MarSik/BuildingAccessSystem/controller/src/include/etl_profile.h

///\file

/******************************************************************************
The MIT License(MIT)

Embedded Template Library.
https://github.com/ETLCPP/etl
https://www.etlcpp.com

Copyright(c) 2017 jwellbelove

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
THE SOFTWARE IS PROVIDED "AS IS", WITHOUT WARRANTY OF ANY KIND, EXPRESS OR
IMPLIED, INCLUDING BUT NOT LIMITED TO THE WARRANTIES OF MERCHANTABILITY,
FITNESS FOR A PARTICULAR PURPOSE AND NONINFRINGEMENT.IN NO EVENT SHALL THE
AUTHORS OR COPYRIGHT HOLDERS BE LIABLE FOR ANY CLAIM, DAMAGES OR OTHER
LIABILITY, WHETHER IN AN ACTION OF CONTRACT, TORT OR OTHERWISE, ARISING FROM,
OUT OF OR IN CONNECTION WITH THE SOFTWARE OR THE USE OR OTHER DEALINGS IN THE
SOFTWARE.
******************************************************************************/

#ifndef __ETL_GCC__
#define __ETL_GCC__

//*****************************************************************************
// GCC
//*****************************************************************************

#include <limits.h>

#define ETL_TARGET_DEVICE_GENERIC
#define ETL_TARGET_OS_NONE
#define ETL_COMPILER_GCC
#define ETL_CPP11_SUPPORTED                        (__cplusplus >= 201103L)
#define ETL_CPP14_SUPPORTED                        (__cplusplus >= 201402L)
#define ETL_NO_NULLPTR_SUPPORT                     !ETL_CPP11_SUPPORTED
#define ETL_NO_LARGE_CHAR_SUPPORT                  !ETL_CPP11_SUPPORTED
#define ETL_CPP11_TYPE_TRAITS_IS_TRIVIAL_SUPPORTED ETL_CPP14_SUPPORTED
#define ETL_ATOMIC_SUPPORTED                       ETL_CPP11_SUPPORTED

#define ETL_NO_CHECKS

#endif
