MarSik/BuildingAccessSystem/controller/src/countdown.h

#ifndef PROJECT_COUNTDOWN_H
#define PROJECT_COUNTDOWN_H


void initializeCountdown();

void countdown(uint32_t millis);

void countdownAbort();

bool countdownFinished();

#endif //PROJECT_COUNTDOWN_H
